zNitche/pDomovoy/modules/warden/src/main.c

#include <math.h>
#include <stdbool.h>

#include "../includes/bluetooth/core.h"
#include "../includes/callbacks.h"
#include "../includes/core_0.h"
#include "../includes/defines.h"
#include "../includes/globals.h"
#include "../includes/led_blink.h"
#include "../includes/voltmeter.h"
#include "hardware/adc.h"
#include "pd_common_config.h"
#include "pdomovoy_common/bluetooth.h"
#include "pdomovoy_common/button.h"
#include "pdomovoy_common/debug_print.h"
#include "pdomovoy_common/pwm.h"
#include "pdomovoy_common/queue.h"
#include "pdomovoy_common/version.h"
#include "pdomovoy_common/voltmeter.h"
#include "pico/cyw43_arch.h"
#include "pico/multicore.h"
#include "pico/stdlib.h"
#include "pico/util/queue.h"

void init_peripherals() {
    // BUZZER
    setup_alarm_pwm_irq_callback(PD_BUZZER_PIN, alarm_buzzer_irq_callback);

    // BUTTON
    init_button_irq(PD_ACTION_BUTTON_PIN, true);
    gpio_set_irq_callback(&gpio_irq_callback);

    // LED
    gpio_init(PD_STATUS_LED_PIN);
    gpio_set_dir(PD_STATUS_LED_PIN, true);
}

void init_mc_queues() {
    queue_init(&g_core0_events_queue, sizeof(MulticoreEvent), 5);
    queue_init(&g_core1_events_queue, sizeof(MulticoreEvent), 5);
}

void init_bluetooth() {
    init_ble();
    turn_bluetooth_on();

    pd_start_bt_queue_processing_loop_bg(&g_bt_functions_queue_timer);
}

int main() {
    stdio_init_all();

    if (DEBUG) {
        // DEBUG waiting for input
        getchar();
    }

    if (cyw43_arch_init()) {
        printf("failed to initialise cyw43\n");
        return 1;
    }

    debug_print("[pD - WARDEN] %s\n", WARDEN_VERSION);

    adc_init();
    start_voltmeter_bg();

    init_peripherals();
    init_mc_queues();

    if (PD_WARDEN_BT_MODE_ENABLED) {
        debug_print("Warden BT mode enabled %s\n");

        pd_init_queue(&g_bt_functions_queue, 5);
        init_bluetooth();
    }

    cyw34_blink_untill_start(-1000, &g_onboard_led_blink_timer, true);

    // core_0 for device handling
    core_0();

    cyw34_blink_untill_stop(&g_onboard_led_blink_timer);
    stop_voltmeter_bg();

    return 0;
}
