zNitche/pDomovoy/modules/warden/src/cores/core_1.c

#include "../../includes/core_1.h"

#include <math.h>
#include <stdbool.h>

#include "../../includes/acceleration_readings.h"
#include "../../includes/defines.h"
#include "../../includes/globals.h"
#include "pdomovoy_common/debug_print.h"
#include "pdomovoy_common/types.h"
#include "pico/stdlib.h"
#include "pico/util/queue.h"
#include "pico_adxl345/adxl345.h"

void _send_event_to_core_0(enum DeviceStatus status) {
    MulticoreEvent event;
    event.status = status;

    queue_add_blocking(&g_core0_events_queue, &event);
}

void _get_initial_accel_mean(ADXL345I2C* adxl345_i2c,
                             AccelerometerReading* output) {
    const size_t readings_count = PD_ACCELERATION_INITIAL_READINGS_COUNT;
    AccelerometerReading total_accel[readings_count] = {};

    get_bunch_of_accel_readings(adxl345_i2c, total_accel, readings_count,
                                PD_ACCELERATION_INITIAL_READINGS_DELAY);

    *output = get_accel_readings_mean(total_accel, readings_count);
}

bool _check_for_trigger_for_axis(float initial_mean, float mean,
                                 float trigger_factor) {

    return fabs(initial_mean - mean) > trigger_factor;
}

bool _check_for_alarm_trigger(ADXL345I2C* adxl345_i2c,
                              AccelerometerReading* initial_accel_mean) {
    const size_t readings_count = PD_ACCELERATION_READINGS_COUNT;
    const float trigger_factor = PD_ACCELERATION_CHANGE_TRIGGER_FACTOR;

    AccelerometerReading total_accel[readings_count];

    get_bunch_of_accel_readings(adxl345_i2c, total_accel, readings_count,
                                PD_ACCELERATION_READINGS_DELAY);
    AccelerometerReading accel_mean =
        get_accel_readings_mean(total_accel, readings_count);

    bool is_triggered = false;

    is_triggered = _check_for_trigger_for_axis(initial_accel_mean->x,
                                               accel_mean.x, trigger_factor);

    if (is_triggered) {
        return true;
    }

    is_triggered = _check_for_trigger_for_axis(initial_accel_mean->y,
                                               accel_mean.y, trigger_factor);

    if (is_triggered) {
        return true;
    }

    is_triggered = _check_for_trigger_for_axis(initial_accel_mean->z,
                                               accel_mean.z, trigger_factor);

    if (is_triggered) {
        return true;
    }

    return false;
}

void core_1() {
    AccelerometerReading initial_accel_mean = {};

    ADXL345I2C adxl345_i2c = {i2c0, 0x53, PD_ADXL345_SDA_PIN,
                              PD_ADXL345_SCL_PIN};

    adxl345_setup_i2c(adxl345_i2c);
    bool connected = adxl345_check_connection(adxl345_i2c);

    if (!connected) {
        _send_event_to_core_0(PD_ADXL345_ERROR);

        return;
    } else {
        _send_event_to_core_0(PD_ADXL345_OK);
    }

    _send_event_to_core_0(PD_STANDBY_PREP);

    adxl345_set_measurements_range(adxl345_i2c, ADXL345_RANGE_4G);
    adxl345_start_measurements(adxl345_i2c);

    debug_print("[core_1] adxl345 has been started\n");

    _get_initial_accel_mean(&adxl345_i2c, &initial_accel_mean);

    debug_print("intial accel_mean = x:%f y:%f z:%f\n", initial_accel_mean.x,
                initial_accel_mean.y, initial_accel_mean.z);

    debug_print(
        "[core_1] got initial acceleration readings, running mainloop\n");

    _send_event_to_core_0(PD_STANDBY_READY);

    while (true) {
        if (_check_for_alarm_trigger(&adxl345_i2c, &initial_accel_mean)) {
            _send_event_to_core_0(PD_ACCELERATION_TRIGGER);
            debug_print("[core_1] alarm trigger\n");

            break;
        }
    }

    adxl345_stop_measurements(adxl345_i2c);
    debug_print("[core_1] exiting...\n");

    return;
}
