zNitche/pDomovoy/modules/trumpet/src/cores/core_0.c

#include "../../includes/core_0.h"

#include "../../includes/defines.h"
#include "../../includes/display.h"
#include "../../includes/globals.h"
#include "../../includes/i2c_devices.h"
#include "../../includes/pages.h"
#include "../../includes/types.h"
#include "pdomovoy_common/debug_print.h"
#include "pdomovoy_common/pwm.h"
#include <stdio.h>

void process_current_page(SSD1306_Frame* frame) {
    PageData* current_page = get_current_page();

    ssd1306_render_string(frame, 0, 0, "*", 0, false);
    ssd1306_render_string(frame, 16, 0, current_page->title, 2, false);
    ssd1306_render_string(frame, 119, 0, "*", 0, false);

    if (current_page->handler != NULL) {
        current_page->handler(frame);
    }
}

void handle_alarm_buzzer() {
    if (g_alarm_state == ALARM_STATE_TRIGGERED) {
        if (!g_alarm_buzzer_on) {
            enable_pwm_irq_on_pin(PD_BUZZER_PIN);
            g_alarm_buzzer_on = true;
        }
    } else {
        if (g_alarm_buzzer_on) {
            disable_pwm_irq_on_pin(PD_BUZZER_PIN);
            g_alarm_buzzer_on = false;
        }
    }
}

void core_0() {
    debug_print("[core_0] started, waiting\n");

    g_aht20_i2c = init_aht20();
    g_ssd1306_i2c = init_ssd1306();

    SSD1306_Frame frame;

    while (true) {
        handle_alarm_buzzer();

        // handle display
        if (!g_display_off) {
            ssd1306_prepare_frame(&frame);

            process_current_page(&frame);
            ssd1306_render(g_ssd1306_i2c, &frame);

            screen_saver_check();
        }

        sleep_ms(500);
    }

    return;
}
