zNitche/pDomovoy/modules/common/src/button.c

#include "pdomovoy_common/button.h"

#include "pdomovoy_common/types.h"
#include <stdbool.h>

#include "pico/time.h"

void init_button_irq(uint gpio, bool pull_down) {
    gpio_init(gpio);
    gpio_set_dir(gpio, GPIO_IN);

    if (pull_down) {
        gpio_pull_down(gpio);
    } else {
        gpio_pull_up(gpio);
    }

    gpio_set_irq_enabled(
        gpio, GPIO_IRQ_EDGE_RISE | GPIO_IRQ_EDGE_FALL | GPIO_IRQ_LEVEL_HIGH,
        true);
}

bool debounce_push_button(uint32_t event, int min_delay_between_clicks,
                          ButtonDebounceCtx* debounce_ctx) {
    if (event == GPIO_IRQ_LEVEL_HIGH && debounce_ctx->is_pressed) {
        return false;
    }

    const uint32_t current_time = to_ms_since_boot(get_absolute_time());

    if (current_time - debounce_ctx->last_call <= min_delay_between_clicks) {
        return false;
    }

    if (event == GPIO_IRQ_EDGE_FALL) {
        debounce_ctx->is_pressed = false;
        debounce_ctx->last_call = current_time;

        return false;
    }

    if (event == GPIO_IRQ_EDGE_RISE && debounce_ctx->is_pressed) {
        debounce_ctx->last_call = current_time;
        return false;
    }

    debounce_ctx->is_pressed = true;
    debounce_ctx->last_call = current_time;

    return true;
}

void count_clicks_in_row(uint32_t* last_click_time, int* clicks_in_row,
                         int min_time_between_clicks) {
    const uint32_t current_click_time = to_ms_since_boot(get_absolute_time());

    if (current_click_time - *last_click_time <= min_time_between_clicks) {
        *clicks_in_row += 1;
    } else {
        *clicks_in_row = 0;
    }

    *last_click_time = current_click_time;
}
