zNitche/pDomovoy/modules/common/src/debug_print.c

#include "pdomovoy_common/debug_print.h"
#include <stdarg.h>
#include <stdio.h>

void debug_print(const char* format, ...) {
#ifdef DEBUG
    if (!DEBUG) {
        return;
    }
#endif

    va_list args;
    va_start(args, format);

    vprintf(format, args);
    va_end(args);
}
