zNitche/pDomovoy/modules/warden/src/utils/debug_print.c

#include "../../includes/debug_print.h"
#include "../../includes/defines.h"
#include <stdarg.h>
#include <stdio.h>

void debug_print(const char* format, ...) {
    if (!DEBUG) {
        return;
    }

    va_list args;
    va_start(args, format);

    vprintf(format, args);
    va_end(args);
}
